picuino/freqcounter/images/thumbs/IMG_20200406_220000.jpg

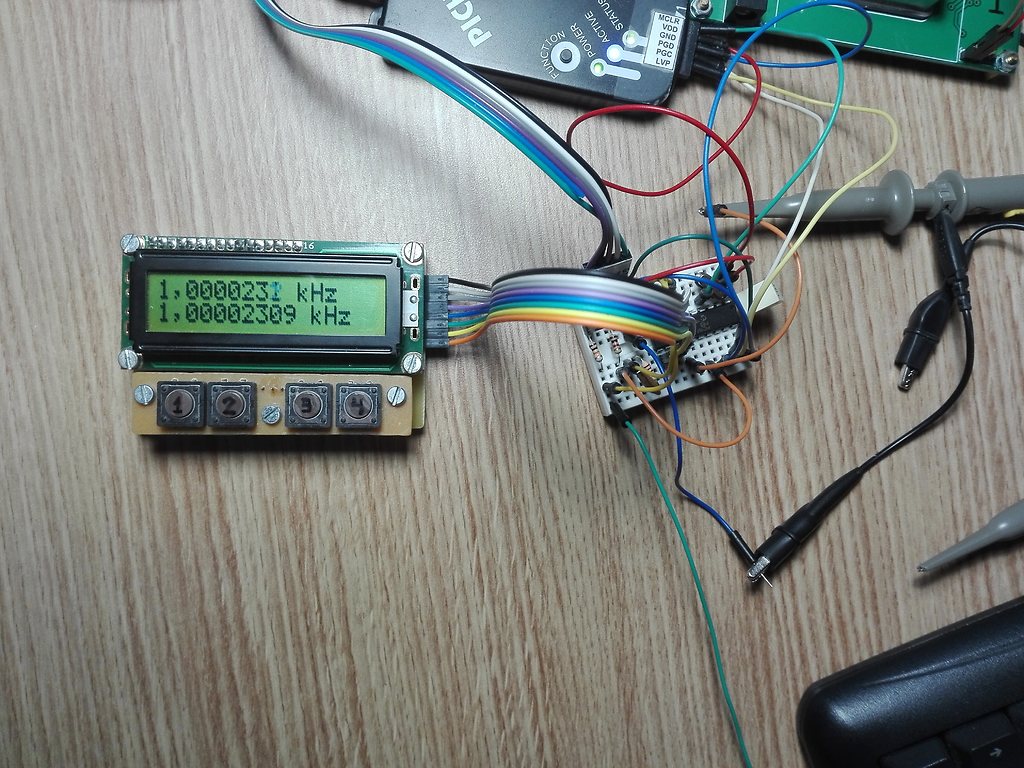
images/thumbs/IMG_20200406_220000.jpg
