picuino/freqcounter/images/thumbs/IMG_20200407_184848.jpg

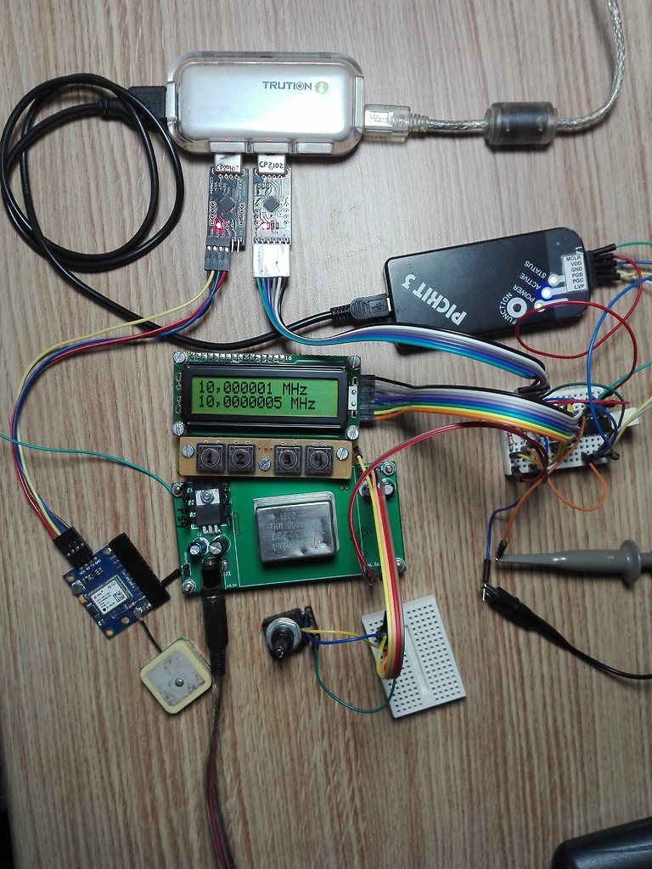
images/thumbs/IMG_20200407_184848.jpg
