picuino/freqcounter/images/thumbs/IMG_20200407_185004.jpg

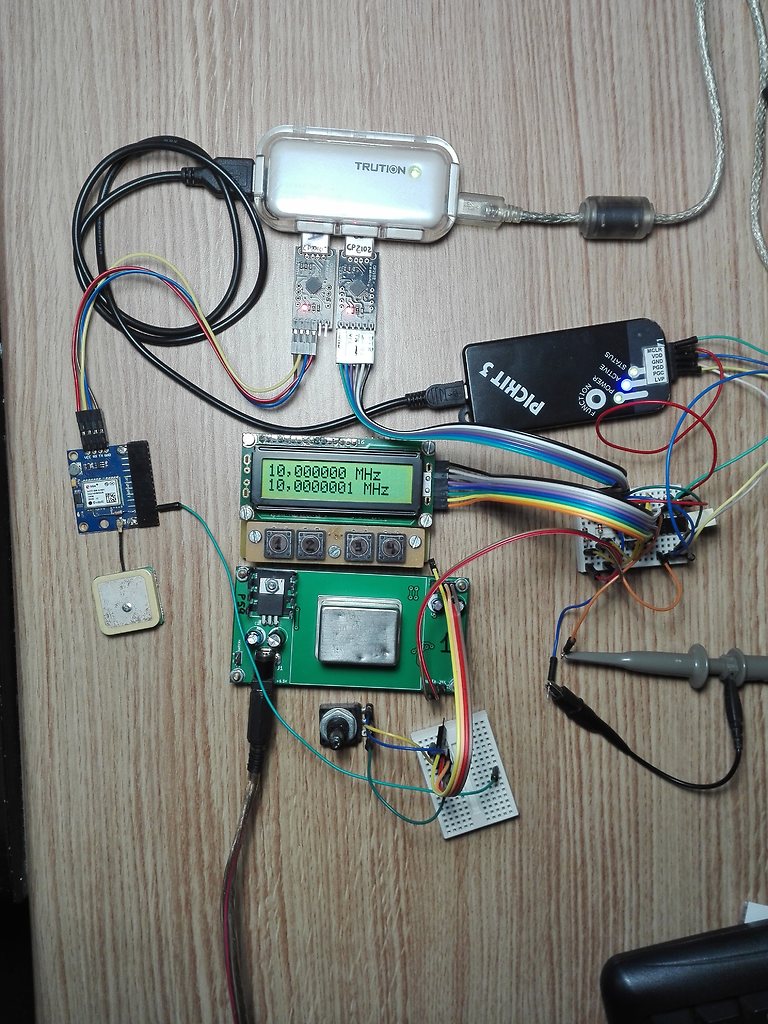
images/thumbs/IMG_20200407_185004.jpg
