picuino/freqcounter/images/thumbs/IMG_20200409_121607.jpg

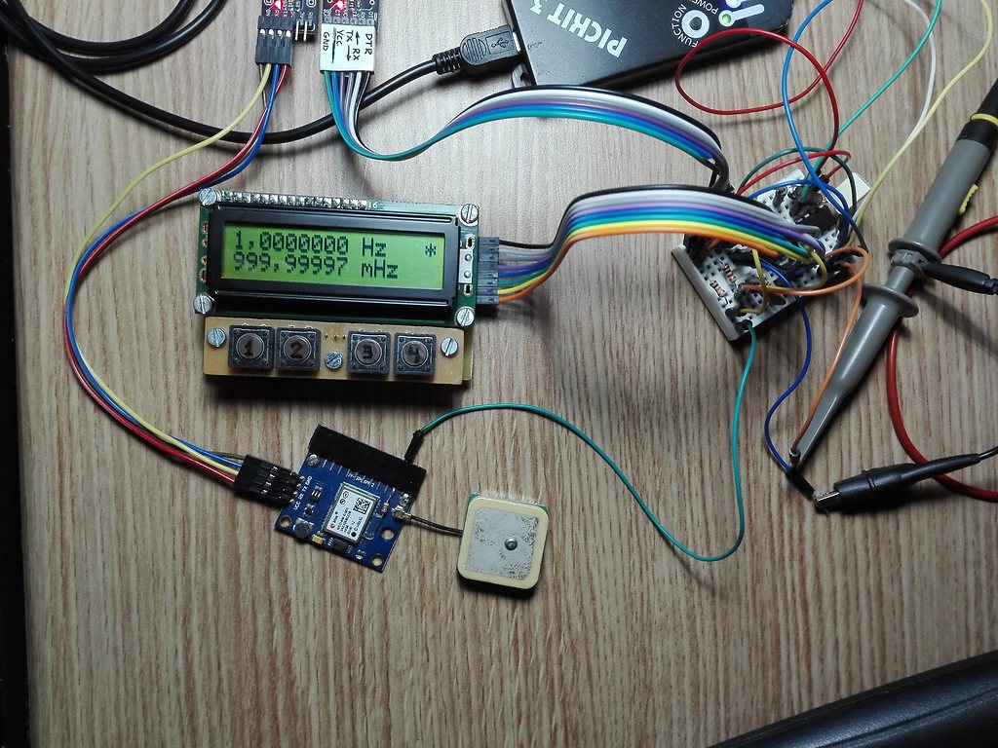
images/thumbs/IMG_20200409_121607.jpg
