picuino/freqcounter/images/thumbs/IMG_20200409_191324.jpg

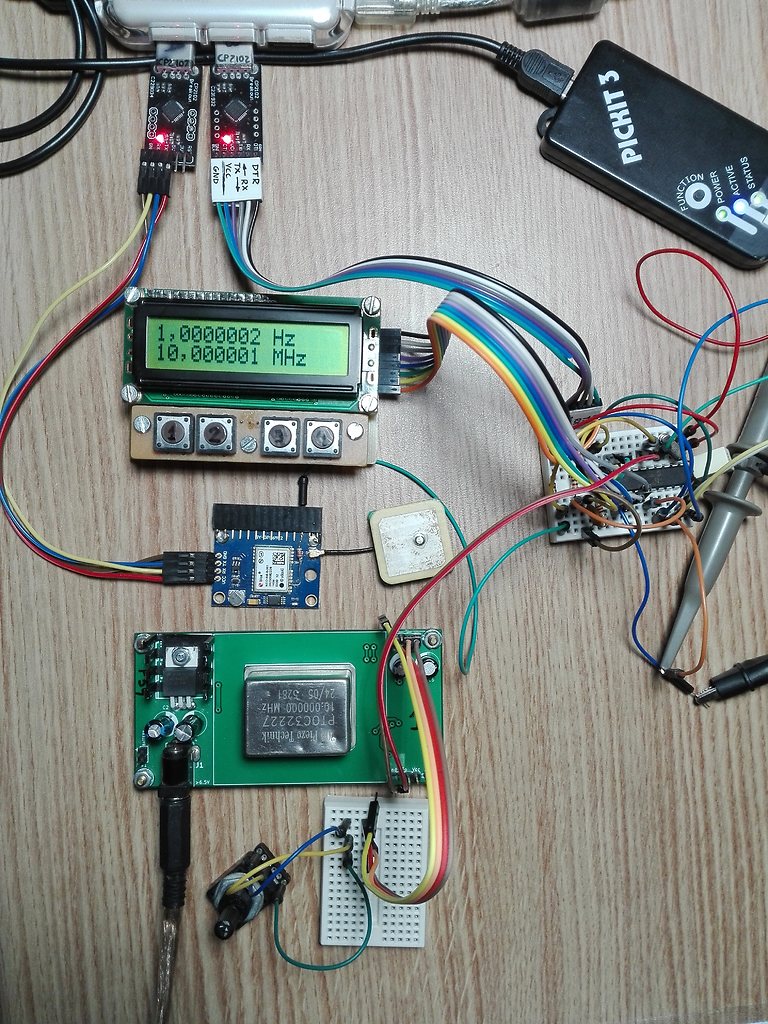
images/thumbs/IMG_20200409_191324.jpg
