picuino/freqcounter/images/thumbs/IMG_20200415_195529.jpg

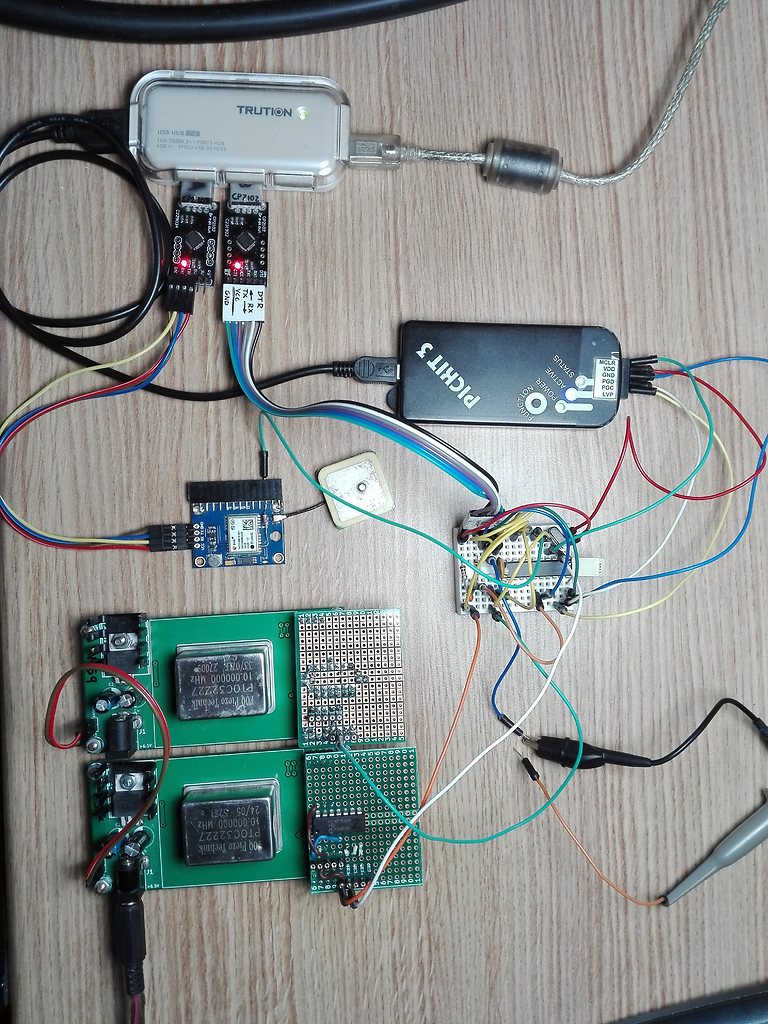
images/thumbs/IMG_20200415_195529.jpg
