picuino/freqcounter/images/thumbs/IMG_20200419_005420.jpg

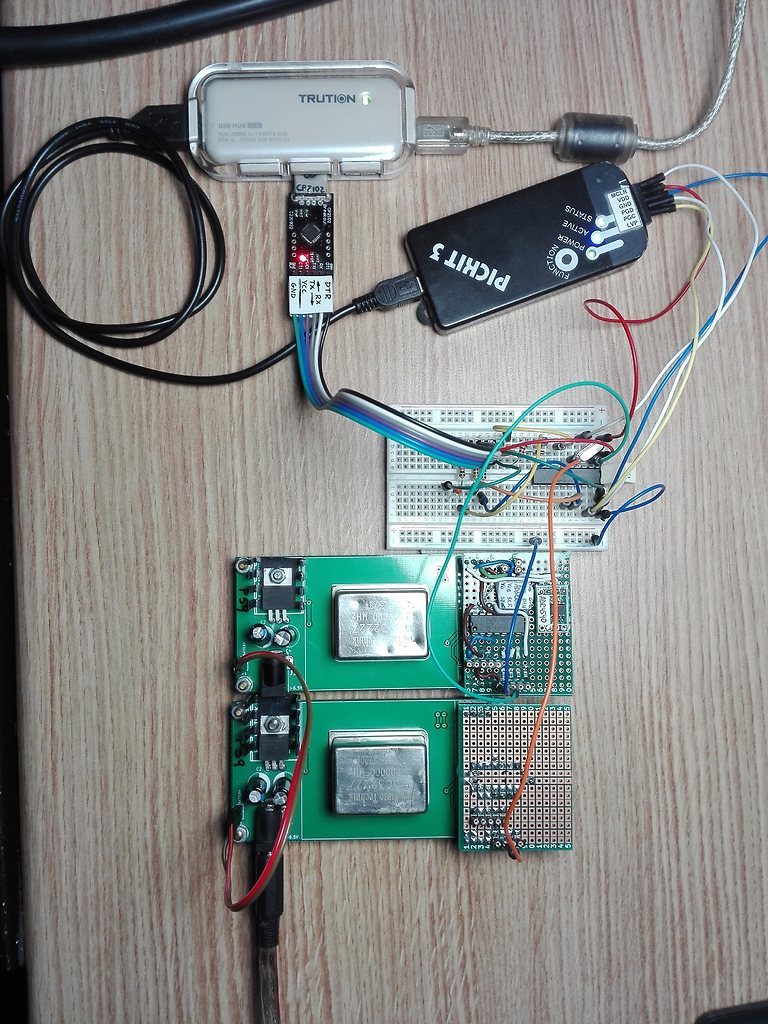
images/thumbs/IMG_20200419_005420.jpg
