picuino/freqcounter/images/thumbs/IMG_20200423_123350.jpg

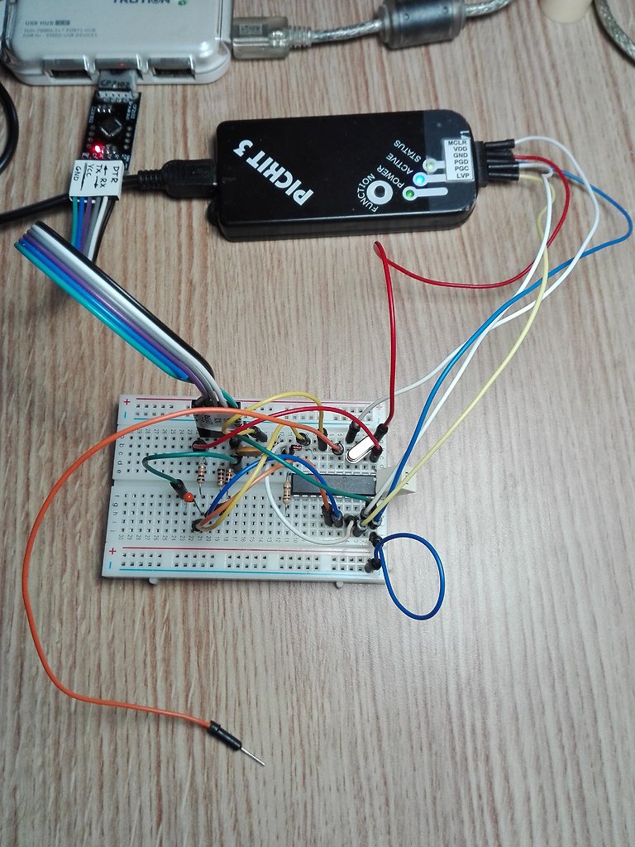
images/thumbs/IMG_20200423_123350.jpg
