picuino/freqcounter/images/thumbs/IMG_20200424_125951.jpg

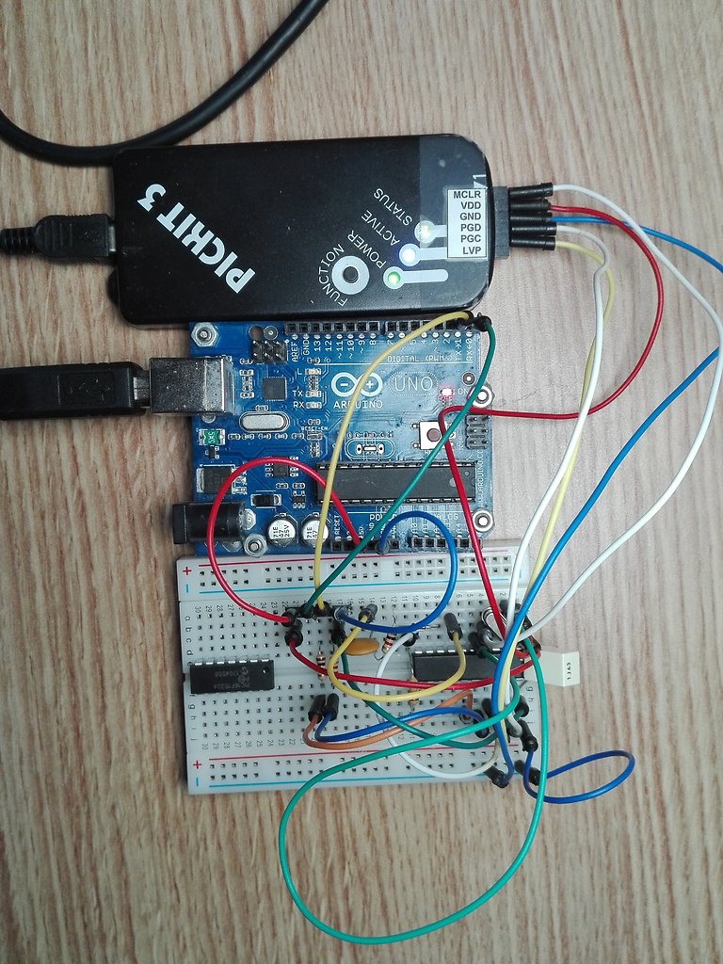
images/thumbs/IMG_20200424_125951.jpg
