picuino/freqcounter/breadboard/kicad/freqcounter_16F18446.sch

## KiCad design breadboard/kicad/freqcounter_16F18446.sch (2020-05-02)

Schematic: freqcounter_16F18446.sch

Parts:
C1: 100nF; C_0805_2012Metric_Pad1.15x1.40mm_HandSolder
C2: 2.2nF; C_0805_2012Metric_Pad1.15x1.40mm_HandSolder
D1: 1N4148; D_SOD-123
J1: ICSP PICKIT
J2: USB-Serial
P1: LCD_DISPLAY_16X2; SIL-16
R1: 10k; R_0805_2012Metric_Pad1.15x1.40mm_HandSolder
R2, R3: 180; R_0805_2012Metric_Pad1.15x1.40mm_HandSolder
R4: 1K; R_0805_2012Metric_Pad1.15x1.40mm_HandSolder
R5: 2k2; R_0805_2012Metric_Pad1.15x1.40mm_HandSolder
U1: PIC16F18446; SOIC-20W_7.5x12.8mm_P1.27mm
Y1: Crystal 8MHz; Crystal_HC18-U_Vertical
