picuino/freqcounter/breadboard/pic16f18446_prog.X/config.h

/*
 *  Configuration parameters
 *
 *  Author: Carlos Pardo
 *
 *  This file is subject to the terms and conditions of the GNU General
 *  Public License Version 3. See the file "COPYING" in the main directory
 *  of this archive for more details.
 *
 */

#define COUNTER_VERSION         "2020-05-02"

#define _FOSC                   32000000UL
#define _FCYCLES                (_FOSC/4)
#define _XTAL_FREQ              _FOSC
#define UART_BAUD               115200


#define MAX_CALIBRATION         300000   // Maximun calibration in PPB
#define SAF_ADDRESS             0x3F80   // Storage Area Flash address

#define DOT_CHAR                '.'

/*
 *  PIC16F18446 Configuration Bit Settings
 */
// CONFIG1
#pragma config FEXTOSC = HS     // External Oscillator mode selection bits (Oscillator not enabled)
#pragma config RSTOSC = EXT4X   // Power-up default value for COSC bits (HFINTOSC = 32MHz)
#pragma config CLKOUTEN = ON   // Clock Out Enable bit (CLKOUT function is disabled; i/o or oscillator function on OSC2)
#pragma config CSWEN = ON       // Clock Switch Enable bit (Writing to NOSC and NDIV is allowed)
#pragma config FCMEN = OFF      // Fail-Safe Clock Monitor Enable bit (FSCM timer enabled)

// CONFIG2
#pragma config MCLRE = ON       // Master Clear Enable bit (MCLR pin is Master Clear function)
#pragma config LPBOREN = OFF    // Low-Power BOR enable bit (ULPBOR disabled)
#pragma config BOREN = ON       // Brown-out reset enable bits (Brown-out Reset Enabled, SBOREN bit is ignored)
#pragma config BORV = LO        // Brown-out Reset Voltage Selection (Brown-out Reset Voltage (VBOR) set to 1.9V on LF, and 2.45V on F Devices)
#pragma config ZCD = OFF        // Zero-cross detect disable (Zero-cross detect circuit is disabled at POR.)
#pragma config PPS1WAY = OFF    // Peripheral Pin Select one-way control (The PPSLOCK bit can be cleared and set only once in software)
#pragma config STVREN = ON      // Stack Overflow/Underflow Reset Enable bit (Stack Overflow or Underflow will cause a reset)

// CONFIG3
#pragma config WDTCPS = WDTCPS_31// WDT Period Select bits (Divider ratio 1:65536; software control of WDTPS)
#pragma config WDTE = OFF        // WDT operating mode (WDT enabled regardless of sleep; SWDTEN ignored)
#pragma config WDTCWS = WDTCWS_7// WDT Window Select bits (window always open (100%); software control; keyed access not required)
#pragma config WDTCCS = SC      // WDT input clock selector (Software Control)

// CONFIG4
#pragma config BBSIZE = BB512   // Boot Block Size Selection bits (512 words boot block size)
#pragma config BBEN = OFF       // Boot Block Enable bit (Boot Block disabled)
#pragma config SAFEN = ON       // Storage Area Flash (SAF) enable bit
#pragma config WRTAPP = OFF     // Application Block Write Protection bit (Application Block not write protected)
#pragma config WRTB = OFF       // Boot Block Write Protection bit (Boot Block not write protected)
#pragma config WRTC = OFF       // Configuration Register Write Protection bit (Configuration Register not write protected)
#pragma config WRTSAF = OFF     // Storage Area Flash Write Protection bit (SAF not write protected)
#pragma config LVP = OFF        // Low Voltage Programming Enable bit (Low Voltage programming enabled. MCLR/Vpp pin function is MCLR.)

// CONFIG5
#pragma config CP = OFF         // UserNVM Program memory code protection bit (UserNVM code protection disabled)
